bogzag/AEMC/Layout/evolution/1.jpeg

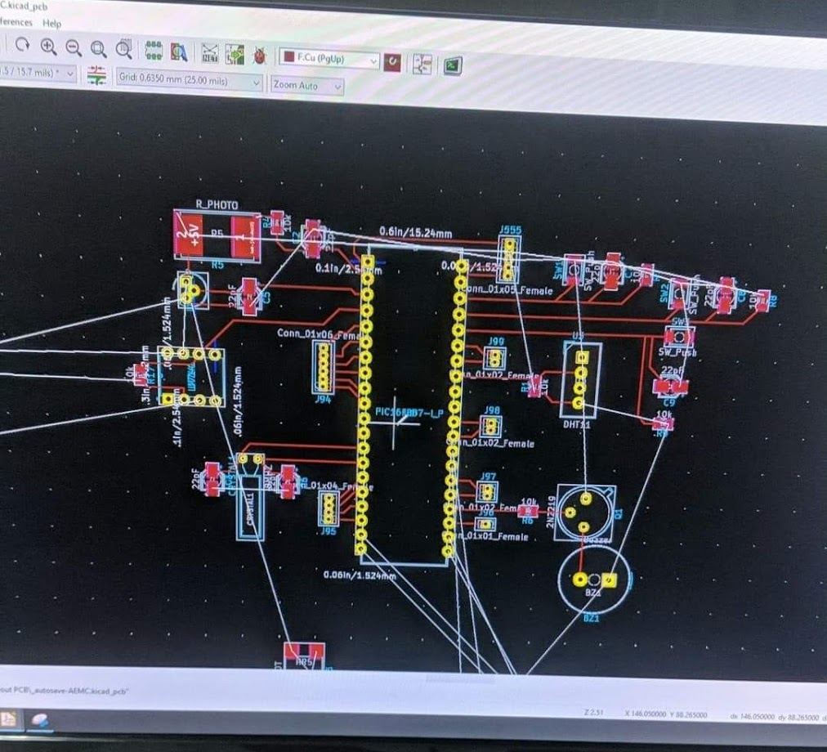
Layout/evolution/1.jpeg
