bogzag/AEMC/Layout/evolution/2.png

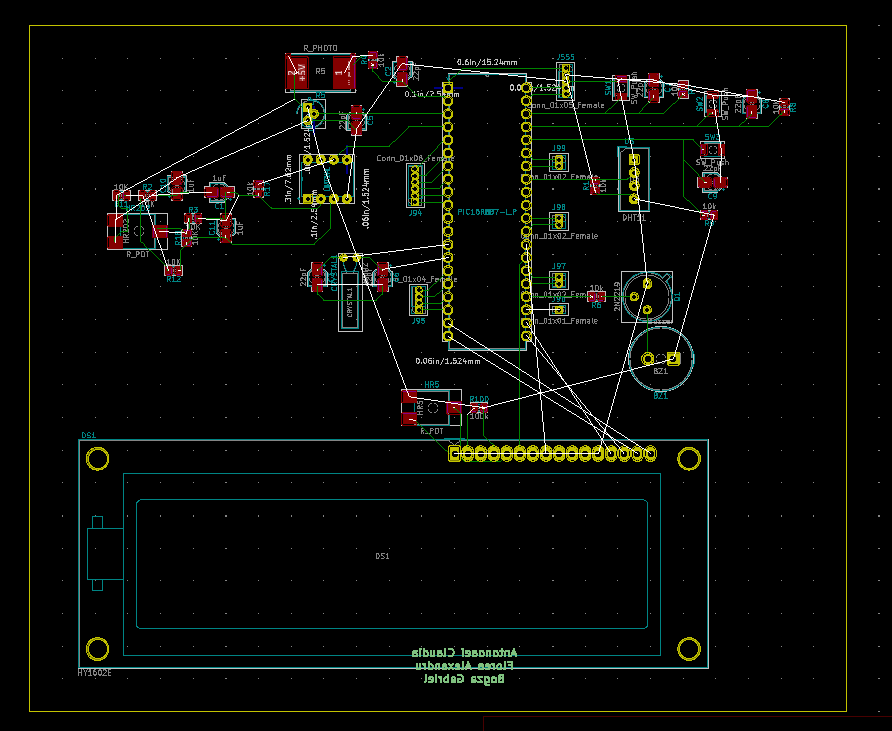
Layout/evolution/2.png
