bogzag/AEMC/Layout/evolution/3.png

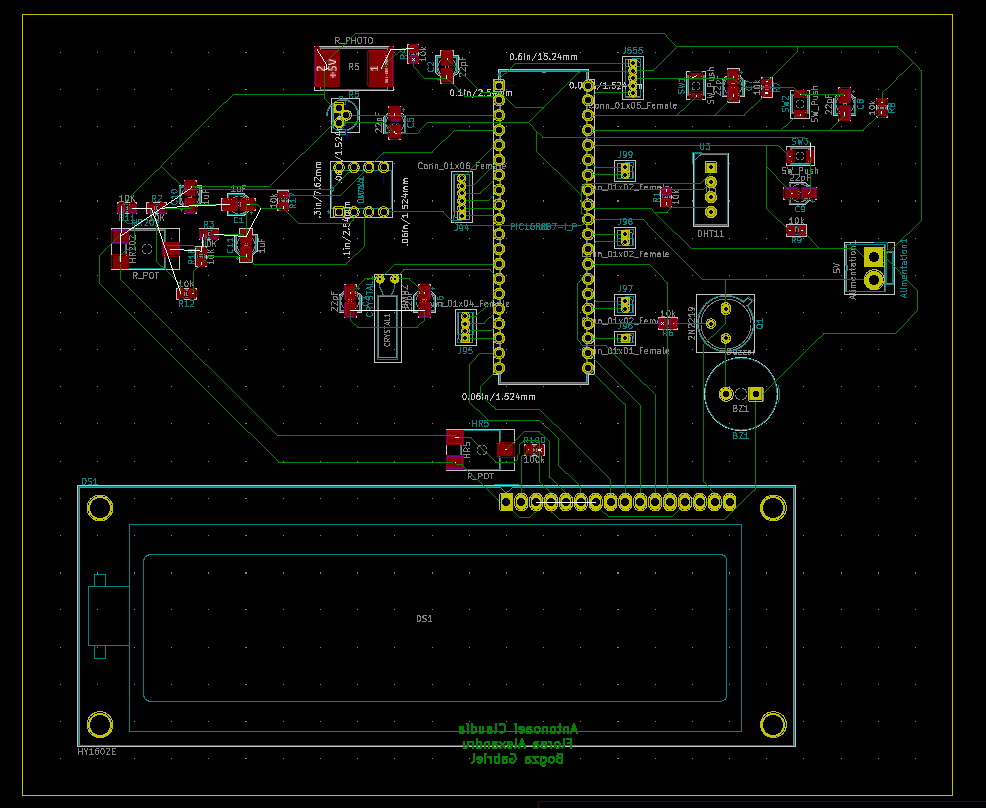
Layout/evolution/3.png
