bogzag/AEMC/Layout/evolution/4.jpeg

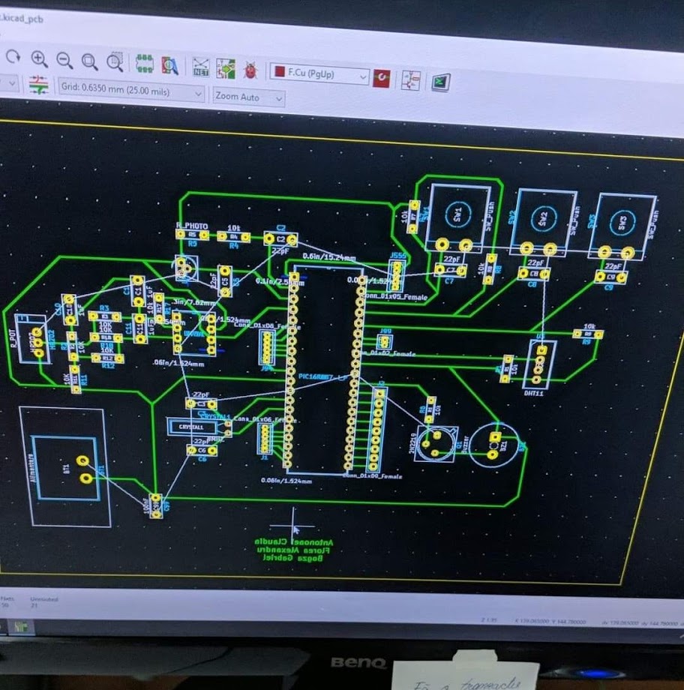
Layout/evolution/4.jpeg
