bogzag/AEMC/Layout/evolution/5.png

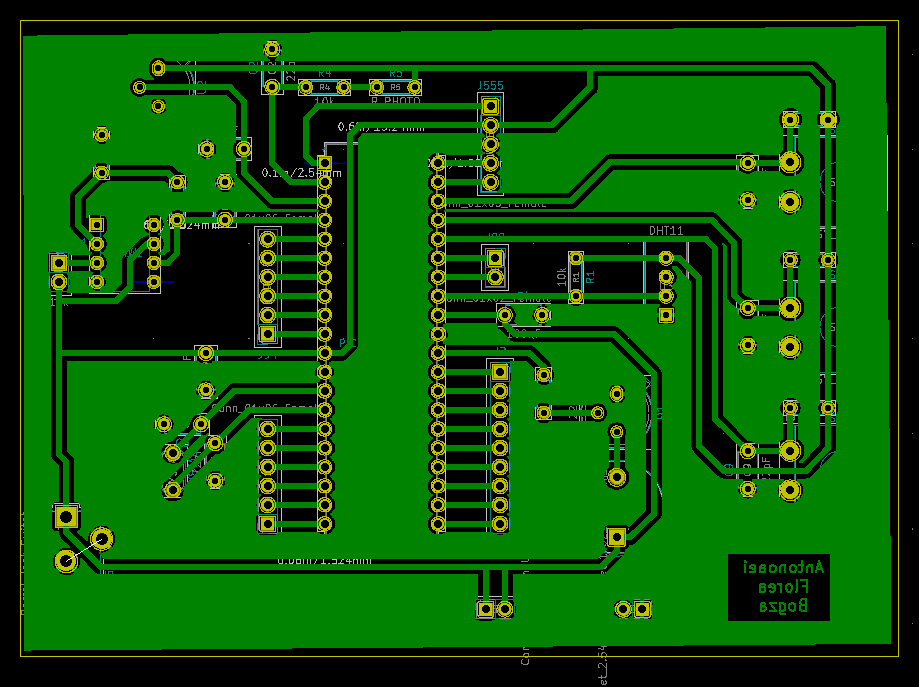
Layout/evolution/5.png
