bogzag/AEMC/PozeProiect/Schematic/20200318_112228.jpg

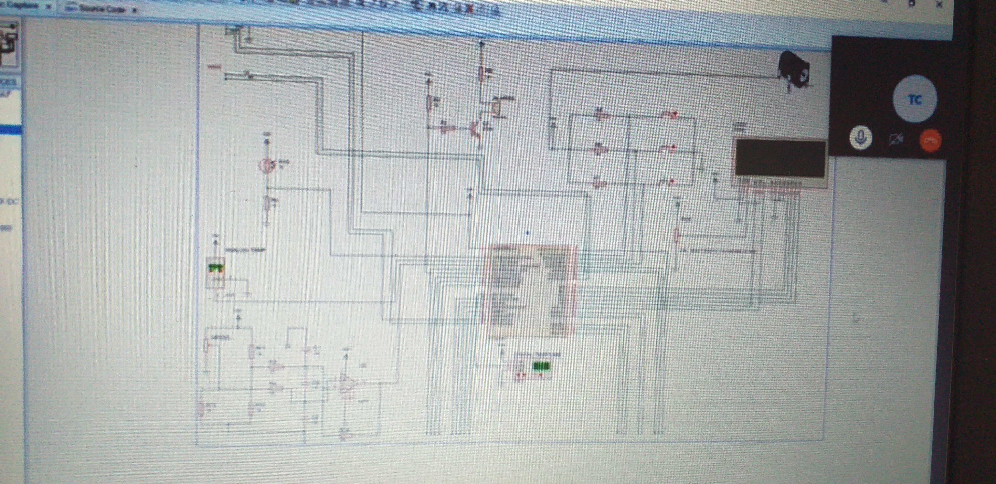
PozeProiect/Schematic/20200318_112228.jpg
